redhawk668/Atari-CO60472-Delay-Line-Replacement/IMG_20201123_210650_4.jpg

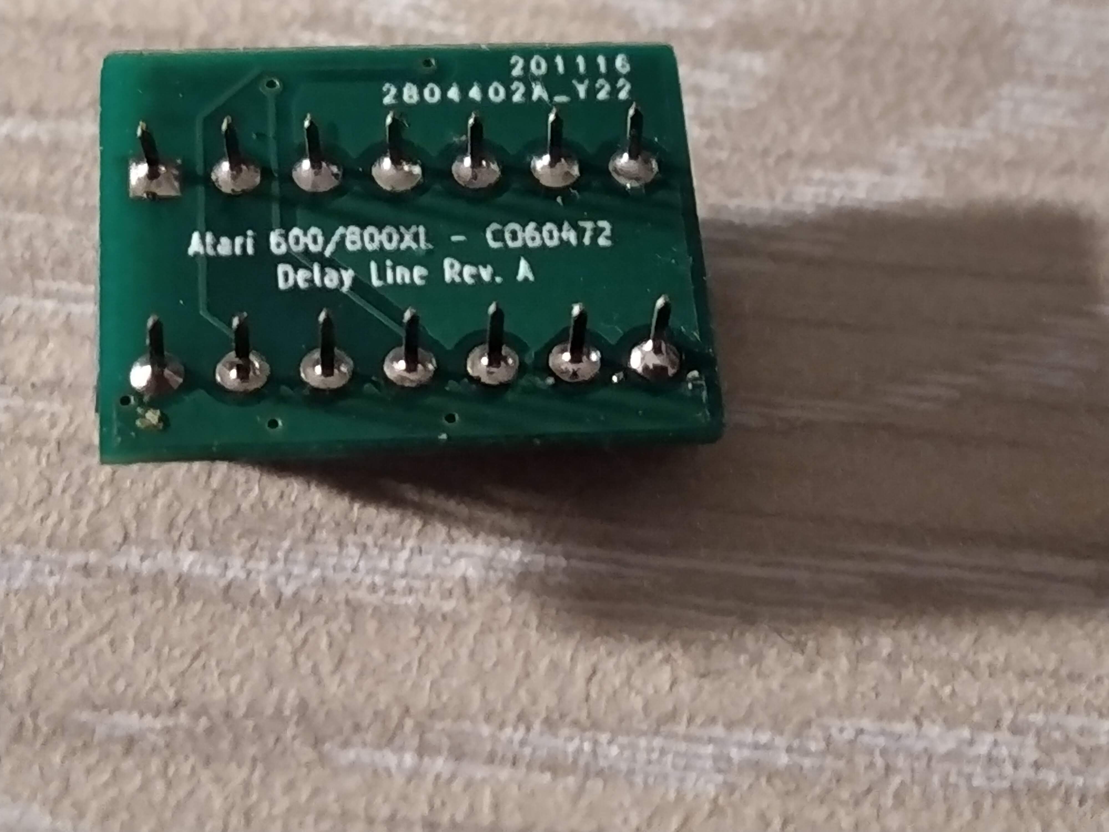
IMG_20201123_210650_4.jpg
